tishyk/Trip_Hub_with_Neo-7m_and_LoRa/cad/pico_a_case/5mm-led.stl

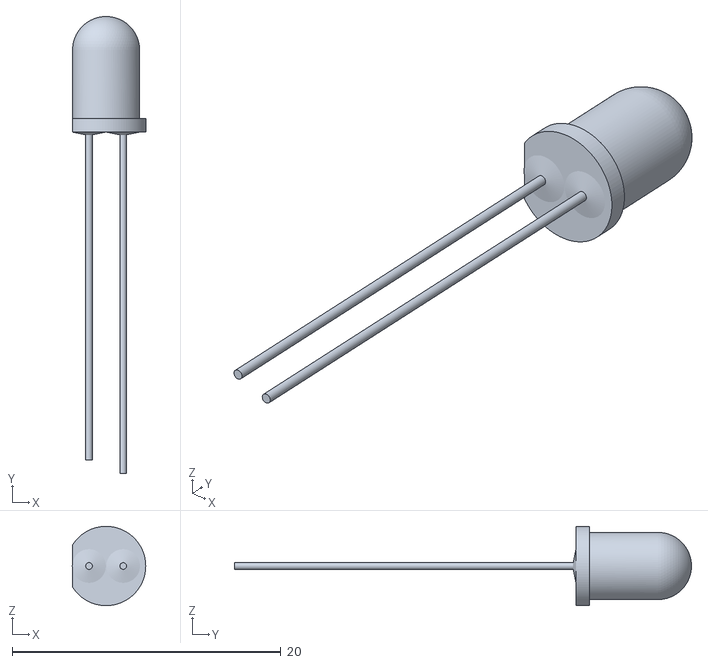
[picture p31: CAD file, 2026-06-12]
cad/pico_a_case/5mm-led.stl
5.47 x 34.0 x 5.90
