tishyk/Trip_Hub_with_Neo-7m_and_LoRa/cad/pico_a_case/RTC DS1302.stl

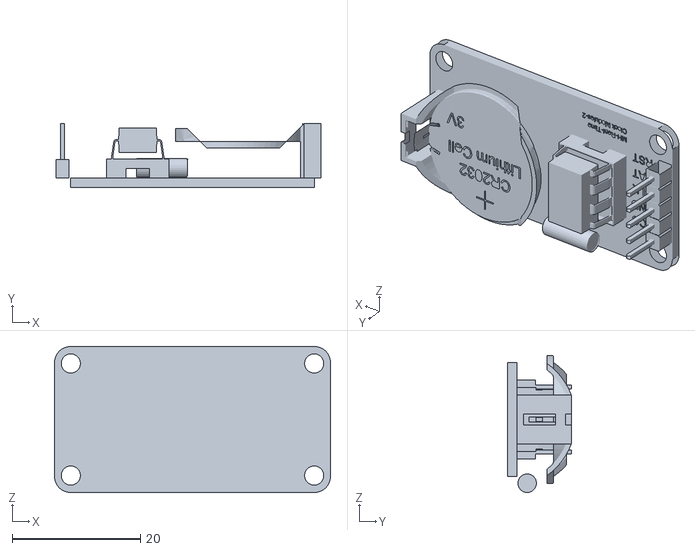
[picture p32: CAD file, 2026-06-12]
cad/pico_a_case/RTC DS1302.stl
43.1 x 10.2 x 22.8
