tishyk/Trip_Hub_with_Neo-7m_and_LoRa/cad/pico_a_case/Pi_Pico_2W_CAD_Reference.stl

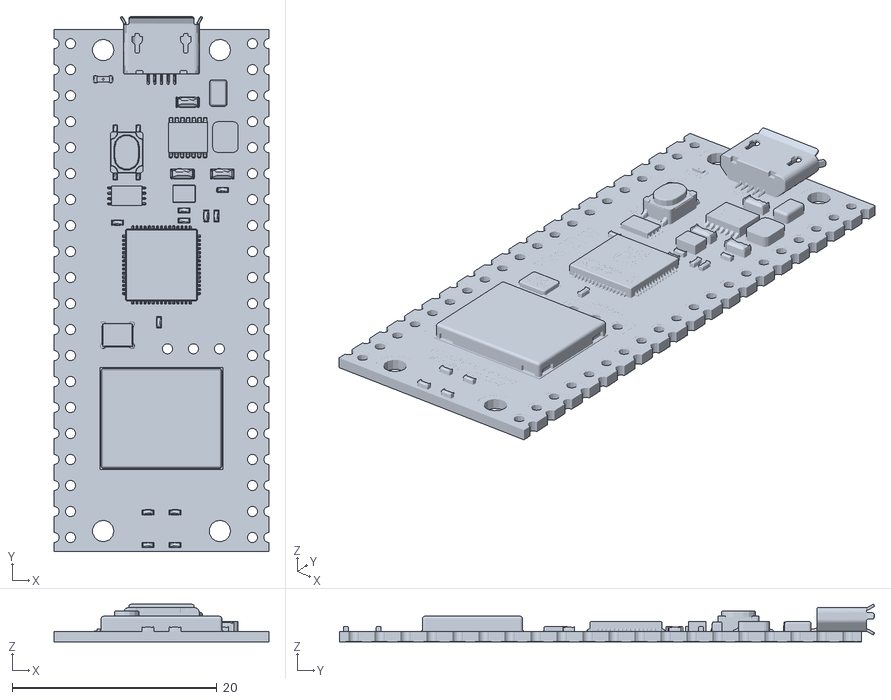
[picture p33: CAD file, 2026-06-12]
cad/pico_a_case/Pi_Pico_2W_CAD_Reference.stl
21.0 x 52.3 x 3.67
