tishyk/Trip_Hub_with_Neo-7m_and_LoRa/cad/pico_a_case/dashboard.stl

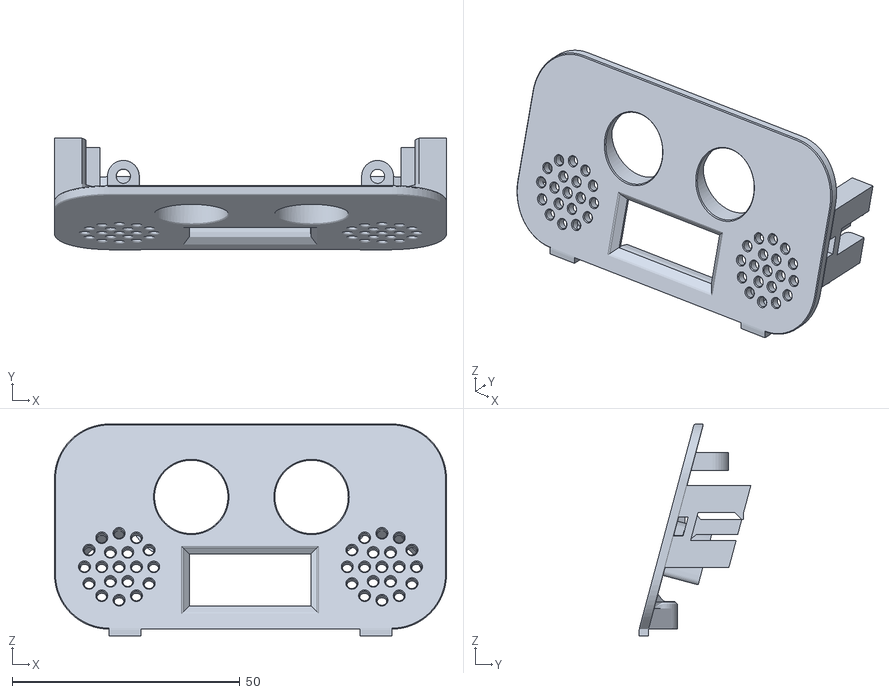
[picture p34: CAD file, 2026-06-12]
cad/pico_a_case/dashboard.stl
86.0 x 24.5 x 46.5
