tishyk/Trip_Hub_with_Neo-7m_and_LoRa/cad/pico_a_case/buzzer.stl

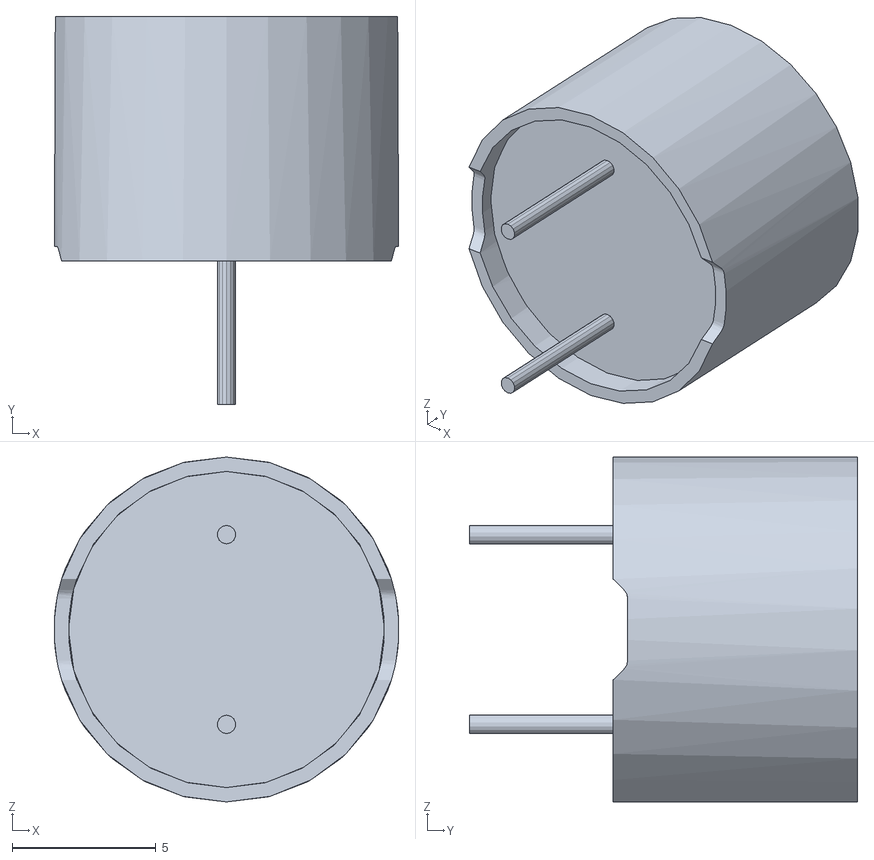
[picture p35: CAD file, 2026-06-12]
cad/pico_a_case/buzzer.stl
12.0 x 13.5 x 12.0
